qppd/safeway/model/SafeWay2.png

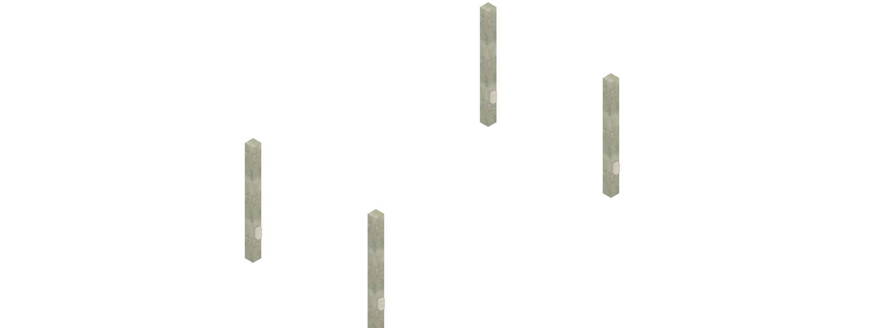
model/SafeWay2.png
