qppd/safeway/model/SafeWay6.png

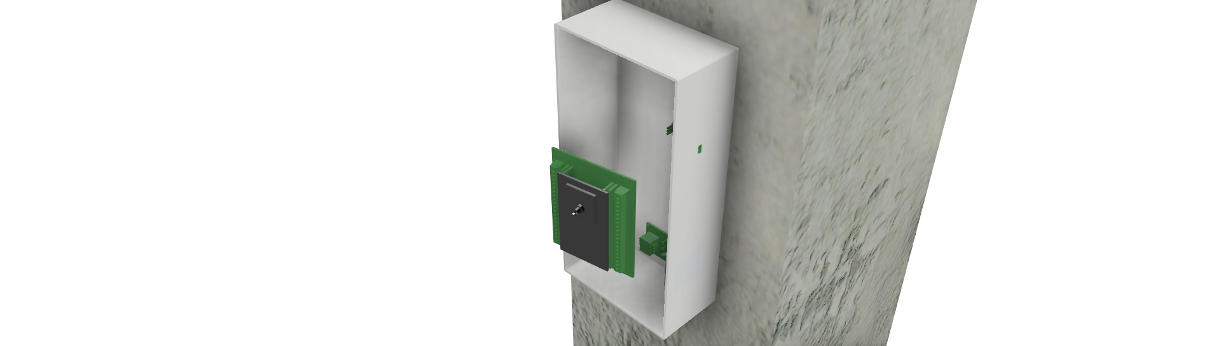
model/SafeWay6.png
